dp-web4/ModuleCPU/SYNCHRONISM_PRINCIPLES.md

# ModuleCPU - Synchronism-Inspired Design Patterns

**Platform**: ATmega64M1 (8-bit AVR with CAN, 64KB flash, 4KB RAM)
**Role**: Middle management layer demonstrating hierarchical coordination

---

## Overview

ModuleCPU's architecture reflects several design patterns that align with principles described in the [Synchronism](https://github.com/dp-web4/Synchronism) framework. While fundamentally a battery management controller, its hierarchical design, autonomous operation, and interface boundaries can be viewed through the lens of distributed intelligence concepts.

This document explores these parallels - not as claims that ModuleCPU "embodies" philosophical principles, but as observations that certain system design patterns recur across scales from philosophy to embedded code.

---

## Design Patterns Aligned with Synchronism Concepts

### 1. Scale-Based Coordination

**Observation**: The module operates at an intermediate scale, coordinating subordinate elements while being coordinated by a superior layer

**Implementation**:
```
Pack Controller (Superior Scale)
    ↓ Provides constraints
ModuleCPU (This Scale)
    ↓ Coordinates subordinates
94 CellCPUs (Subordinate Scale)
```

**Autonomous Behavior at Module Scale**:
- Decides when to poll cells (timing strategy)
- Determines how to aggregate 94 cell readings
- Handles VUART communication errors locally
- Manages state transitions within constraints

**Constraints from Pack** (doesn't micromanage):
- Maximum allowed state (OFF/STANDBY/ACTIVE)
- Balancing permission
- Registration requirement

**Constraints from Cells** (physical limits):
- VUART timing and protocol
- Cell capability limits

**Pattern**: Each scale has autonomy within boundaries set by adjacent scales. This resembles the "scale-based autonomy" concept where each layer operates independently within its context.

---

### 2. Interface Boundaries as Information Filters

**Observation**: ModuleCPU has well-defined interfaces that hide internal complexity

**Upward Interface** (to Pack Controller):
```
Pack Controller sees:
- Module-level aggregates (average temp, voltage spread)
- Module state (OFF/STANDBY/ACTIVE/BALANCE)
- Cell count and communication statistics
- Error flags

Pack Controller does NOT see:
- Individual cell polling sequence
- VUART bit timing details
- Internal state machine transitions
- Individual cell raw data (until requested)
```

**Downward Interface** (to Cells):
```
Cells see:
- VUART requests for data
- Simple protocol (position in chain, data requests)

Cells do NOT see:
- CAN bus communication
- Pack Controller existence
- Other modules
- Module's internal decision logic
```

**Pattern**: These interface boundaries can be understood as analogous to "Markov blankets" - each layer sees only the interface of adjacent layers, not internal states.

---

### 3. Hierarchical Information Aggregation

**Observation**: Information compresses as it moves up the hierarchy

**Data Flow Upward** (Compression):
```
Cell Level: 94 cells × 2 sensors = 188 data points
    ├─ Cell 1: 23.5°C, 3.650V
    ├─ Cell 2: 23.7°C, 3.645V
    ├─ ...
    └─ Cell 94: 23.6°C, 3.655V

    ↓ (Module aggregates)

Module Level: Compressed to ~10 values
    ├─ Avg temp: 23.6°C
    ├─ Min voltage: 3.640V
    ├─ Max voltage: 3.660V
    ├─ Voltage spread: 20mV
    └─ Cell status bitmap

    ↓ (To Pack)

Pack sees: Summary, not raw data
```

**Inverse Command Flow** (Expansion):
```
Pack: "Enter BALANCE state" (1 command)
    ↓ (Module interprets)
Module: Polls 94 cells, sends balancing enable to subset
    ↓ (Cells execute)
Cells: Individual cells activate/deactivate FETs based on local voltage
```

**Pattern**: This asymmetric information flow (aggregation up, expansion down) resembles the hierarchical information dynamics described in distributed systems theory.

---

### 4. Emergent Coordination

**Observation**: System-level behavior emerges from local decisions without centralized control

**Example: Battery Balancing**

**No Central Balancing Controller**:
```c
// Module doesn't command: "Cell 5, balance at 50% duty cycle"
// Instead, module enables balancing context:

void EnableBalancing(void) {
    // Module simply requests cells to check their voltage
    for (uint8_t i = 0; i < cell_count; i++) {
        VUARTPollCell(i);  // Cell decides locally if it needs balancing
    }
}

// Each cell makes LOCAL decision:
// In CellCPU:
// if (my_voltage > threshold) { activate_balancing_FET(); }
```

**Emergent Result**:
- High cells balance (local decision)
- Module coordinates timing (when to poll)
- Pack enables context (permission to balance)
- **System-level balancing emerges** from distributed local decisions

**Pattern**: Intelligence emerges from coordination of simple autonomous elements, rather than centralized command-and-control.

---

### 5. Reality Construction Through Sensor Fusion

**Observation**: Module constructs a "view of reality" by fusing multiple data sources across time

**Temporal Sensor Fusion**:
```
Sensor Inputs (across time):
├─ Cell 1 temp (now): 23.5°C
├─ Cell 1 temp (1s ago): 23.4°C
├─ Cell 1 temp (2s ago): 23.3°C
│   ↓ (fusion across time)
└─ Derived: Temperature rising at 0.1°C/s

Multi-Cell Spatial Fusion:
├─ Cells 1-10 (top of module): 24.2°C average
├─ Cells 11-84 (middle): 23.6°C average
├─ Cells 85-94 (bottom): 23.0°C average
│   ↓ (spatial fusion)
└─ Derived: Thermal gradient of 1.2°C across module
```

**Emergent "Module Health" Concept**:
```c
// Module constructs emergent understanding
bool IsModuleHealthy(void) {
    float temp_avg = CalculateAverageTemp();
    float temp_spread = CalculateMaxTempDelta();
    float voltage_spread = CalculateMaxVoltageDelta();

    // "Health" emerges from fusion of multiple metrics
    return (temp_spread < 5.0) &&     // Temperature uniformity
           (voltage_spread < 0.050) &&  // Voltage balance
           (temp_avg < 60.0);           // Thermal safety
}
```

**Pattern**: Higher-level concepts ("module health") emerge from fusion of lower-level sensor data, similar to how reality might be constructed through sensor fusion in Synchronism's framework.

---

### 6. Intent Propagation Through Scales

**Observation**: System goals propagate through hierarchy, adapted at each scale

**Example: "Charge the Battery" Intent Flow**

```
User Intent: "Charge the battery"
    ↓
Pack Controller: Closes charging contactor, enables modules
    ↓ (propagates as)
Pack Command: "Modules, enter ACTIVE state"
    ↓
ModuleCPU: Transitions to ACTIVE, begins cell monitoring
    ↓ (propagates as)
Module Action: Polls cells, checks for overcharge
    ↓
CellCPU: Measures rising voltage
    ↓ (triggers local intent)
Cell Response: If voltage > threshold, activate balancing
```

**Intent Transforms at Each Scale**:
- **User scale**: "Charge"
- **Pack scale**: "Enable charging circuit"
- **Module scale**: "Monitor cells actively"
- **Cell scale**: "Measure and respond to voltage"

Each scale interprets and adapts the intent appropriate to its context.

---

## Practical Design Insights

These pattern observations lead to concrete design benefits:

### 1. Robustness Through Hierarchy

**Pattern**: Failures are contained within their scale

```
Cell Failure:
├─ Cell 23 stops responding
├─ Module detects missing cell (bitmap update)
├─ Module continues with 93 cells
├─ Pack sees module with reduced capacity
└─ System continues operating (degraded but functional)

Not: Entire system failure from one cell
```

### 2. Flexibility Through Interface Abstraction

**Pattern**: Implementation changes don't propagate across boundaries

```
Change Cell Temperature Sensor (MCP9843 → different sensor):
├─ Cell firmware changes (new I2C protocol)
├─ VUART interface unchanged (still transmits temperature)
├─ Module sees same data format
├─ Pack sees same module interface
└─ System continues working (transparent change)
```

### 3. Testability Through Scale Isolation

**Pattern**: Each scale can be tested independently

```
Module Testing:
├─ Can test with real cells (integration test)
├─ Can test with cell simulators (unit test)
├─ Can test with Pack or standalone (flexible context)
└─ Module logic testable without full system
```

---

## Code Examples Illustrating Patterns

### 1. Autonomous Decision Making (Scale-Based Autonomy)

```c
// Module decides HOW to handle communication errors
// Pack doesn't micromanage retry logic
void PollCellWithRetry(uint8_t cell_index) {
    uint8_t retry_count = 0;

    while (retry_count < MAX_RETRIES) {
        if (VUARTPollCell(cell_index)) {
            // Success - local decision to exit retry loop
            return;
        }

        // Local decision: exponential backoff
        _delay_ms(10 * (1 << retry_count));
        retry_count++;
    }

    // Local decision: mark cell as non-responsive
    UpdateCellStatus(cell_index, CELL_NO_RESPONSE);
}
```

### 2. Information Aggregation (Hierarchical Compression)

```c
// Module compresses 94 cells → summary for Pack
void PrepareModuleStatus(CANMessage* msg) {
    // Aggregate cell data
    float temp_avg = 0, temp_min = 999, temp_max = -999;
    uint16_t volt_min = 65535, volt_max = 0;

    for (uint8_t i = 0; i < cell_count; i++) {
        // Fusion across cells
        temp_avg += cell_temps[i];
        temp_min = min(temp_min, cell_temps[i]);
        temp_max = max(temp_max, cell_temps[i]);
        volt_min = min(volt_min, cell_voltages[i]);
        volt_max = max(volt_max, cell_voltages[i]);
    }
    temp_avg /= cell_count;

    // Pack message: compressed representation
    msg->data[0] = (uint8_t)(temp_avg);
    msg->data[1] = (uint8_t)(temp_max - temp_min);  // Spread, not individuals
    msg->data[2] = volt_min >> 8;
    msg->data[3] = volt_min & 0xFF;
    msg->data[4] = (volt_max - volt_min) >> 8;  // Delta, not absolutes
    msg->data[5] = (volt_max - volt_min) & 0xFF;

    // 188 values compressed to 6 bytes
}
```

### 3. Interface Boundary (Markov Blanket-Style)

```c
// Module's interface to Pack: well-defined, hides internals
void ProcessPackCommand(CANMessage* cmd) {
    switch (cmd->id) {
        case ID_MODULE_STATE_CHANGE:
            // Pack can request state change
            // Module decides if transition is valid
            if (CanTransitionTo(cmd->data[0])) {
                ChangeState(cmd->data[0]);
            } else {
                // Internal logic: reject invalid transition
                SendErrorResponse();
            }
            break;

        case ID_MODULE_STATUS_REQUEST:
            // Pack requests status
            // Module decides what to include based on current state
            SendStatusMessage();
            break;

        // Pack doesn't have commands for:
        // - "Poll cell 23 right now"
        // - "Set VUART timing to X"
        // - "Use this specific aggregation algorithm"
        // Module retains autonomy over internal operations
    }
}
```

---

## Relationship to Synchronism Whitepaper

Readers interested in the theoretical foundations that inform these design patterns may find relevant concepts in the [Synchronism Whitepaper](https://github.com/dp-web4/Synchronism):

- **Section on Intent Dynamics**: How goals propagate and transform across scales
- **Section on Markov Blankets**: Information boundaries and interface design
- **Section on Scale-Based Autonomy**: Hierarchical coordination without micromanagement
- **Section on Sensor Fusion**: How reality emerges from integrated data sources

These are offered as conceptual frameworks that may provide useful lenses for understanding embedded system architecture, not as claims that a battery controller implements abstract philosophy.

---

## Summary

ModuleCPU's design exhibits several patterns that align with concepts from distributed systems theory and the Synchronism framework:

1. **Scale-Based Autonomy**: Module operates independently within constraints
2. **Interface Boundaries**: Well-defined information hiding at each layer
3. **Hierarchical Aggregation**: Information compresses upward, commands expand downward
4. **Emergent Coordination**: System behavior from distributed local decisions
5. **Sensor Fusion**: Higher-level understanding from integrated data
6. **Intent Propagation**: Goals transform appropriately at each scale

These patterns emerged from practical engineering requirements (managing 94 cells efficiently, maintaining robustness, enabling testability) but happen to parallel theoretical concepts in interesting ways.

**Whether viewed as philosophy-in-silicon or simply sound embedded system design, these patterns demonstrably work in production hardware.**
