dp-web4/ModuleCPU/.github/TOPICS.md

# Repository Topics

## Primary Topics
- battery-management-system
- bms
- embedded-systems
- modbatt
- battery

## Platform/Hardware
- atmega64m1
- avr
- can-bus
- module-controller

## Architecture/Patterns
- distributed-intelligence
- hierarchical-control
- aggregation
- virtual-uart
- markov-blanket
- fractal-architecture

## Application Domain
- electric-vehicle
- lithium-ion
- energy-storage
- iot

## Ecosystem/Framework
- web4
- synchronism
- open-source
- agpl-3.0

## Use these topics on GitHub via Settings → Topics
