dp-web4/ModuleCPU/can.c

/* 
 * Module controller firmware - CAN
 *
 * This module contains the CAN bus functionality. 
 *
 */

#include <stdint.h>
#include <xc.h>
#include <stdbool.h>
#include <avr/interrupt.h>
#include <string.h>
#include "main.h"
#include "can.h"
#include "can_ids.h"
#include "vUART.h"  // For vUARTIsBusy()

#define CAN_DISABLED			(0)
#define CAN_TXONLY				(1)
#define CAN_RXONLY				(2)
#define CAN_FBRX				(3)

#define CANMOB_RX_IDX			(0)
#define CANMOB_TX_IDX			(1)

// Timeout for CAN TX in main loop ticks (100ms each)
#define CAN_TX_TIMEOUT_TICKS	(2)	// 200ms timeout

static volatile uint8_t sg_u8Busy;	// 0 = not busy, >0 = busy with timeout countdown
static void (*sg_pfRXCallback)(ECANMessageType eType, uint8_t* pu8Data, uint8_t u8DataLen);

// Maximum size of CAN message
#define CAN_MAX_MSG_SIZE		8

// Last transmit info
static uint8_t sg_u8TransmitAttempts;
static ECANMessageType sg_eLastTXType;
static uint8_t sg_u8LastTXData[CAN_MAX_MSG_SIZE];
static uint8_t sg_u8LastTXDataLen;
static volatile bool sg_bInRetransmit = false;

// Diagnostic counters for CAN issues
static uint16_t sg_u16TxTimeouts = 0;		// Count of TX timeouts
static uint16_t sg_u16TxErrors = 0;		// Count of TX errors recovered
static uint16_t sg_u16TxOkPolled = 0;		// Count of TXOK found by polling
static uint16_t sg_u16BusOffEvents = 0;	// Count of bus-off events
static uint16_t sg_u16ErrorPassive = 0;	// Count of error passive states
static uint8_t sg_u8BusOffRecoveryDelay = 0;	// Delay counter after bus-off recovery
static uint8_t sg_u8TxOnlyErrorCount = 0;	// Count of consecutive TX-only errors
static uint8_t sg_u8TxBackoffDelay = 0;	// Adaptive backoff delay for TX errors

// RX Message Queue - moves heavy processing out of ISR to main loop
#define CAN_RX_QUEUE_SIZE 8
typedef struct {
	ECANMessageType eType;
	uint8_t u8Data[CAN_MAX_MSG_SIZE];
	uint8_t u8DataLen;
} CANRxMessage;

static CANRxMessage sg_rxQueue[CAN_RX_QUEUE_SIZE];
static volatile uint8_t sg_rxQueueHead = 0;
static volatile uint8_t sg_rxQueueTail = 0;
static uint16_t sg_u16RxQueueOverflows = 0;	// Diagnostic: queue overflow count

// MOB Reconfiguration Flags - defers MOB setup to main loop
static volatile bool sg_bMOB0NeedsReconfigure = false;
static volatile bool sg_bMOB2NeedsReconfigure = false;

// TX Retry Flag - defers retry logic to main loop
static volatile bool sg_bRetryPending = false;

typedef struct 
{
	uint8_t u8Mode;
	bool bReplyValid;
	uint16_t u16ID;
	uint16_t u16IDMask;
	bool bRTRTag;
	bool bRTRMask;
} SMOBDef;

static const SMOBDef sg_sMOBDisabled =
{
	CAN_DISABLED,
	false,
	0x7ff,
	0x7ff,
	false,
	false,
};

// Recevie any message with ID 0x5xx (RTR or not)
static const SMOBDef sg_sMOBGenericReceive =
{
	CAN_RXONLY,
	false,
	0x500,
	0x700,  // Mask: 0x700 = bits 10:8 must match, allowing only 0x500-0x5FF
	false,
	false,
};

static const SMOBDef sg_sMOBModuleAnnouncement =
{
	CAN_TXONLY,
	false,
	PKT_MODULE_ANNOUNCEMENT,
	0x7ff,
	false,
	false,
};

static const SMOBDef sg_sMOBModuleStatus1 =
{
	CAN_TXONLY,
	false,
	PKT_MODULE_STATUS1,
	0x7ff,
	false,
	false,
};

static const SMOBDef sg_sMOBModuleStatus2 =
{
	CAN_TXONLY,
	false,
	PKT_MODULE_STATUS2,
	0x7ff,
	false,
	false,
};

static const SMOBDef sg_sMOBModuleStatus3 =
{
	CAN_TXONLY,
	false,
	PKT_MODULE_STATUS3,
	0x7ff,
	false,
	false,
};

static const SMOBDef sg_sMOBModuleCellCommStat1 =
{
	CAN_TXONLY,
	false,
	PKT_MODULE_CELL_COMM_STAT1,
	0x7ff,
	false,
	false,
};

static const SMOBDef sg_sMOBModuleCellCommStat2 =
{
	CAN_TXONLY,
	false,
	PKT_MODULE_CELL_COMM_STAT2,
	0x7ff,
	false,
	false,
};

static const SMOBDef sg_sMOBModuleCellDetail = 
{
	CAN_TXONLY,
	false,
	PKT_MODULE_CELL_DETAIL,
	0x7ff,
	false,
	false,
};

static const SMOBDef sg_sMOBModuleHardwareDetail = 
{
	CAN_TXONLY,
	false,
	PKT_MODULE_HARDWARE,
	0x7ff,
	false,
	false,
};

static const SMOBDef sg_sMOBModuleRequestTime =
{
	CAN_TXONLY,
	false,
	PKT_MODULE_REQUEST_TIME,
	0x7ff,
	false,
	false,
};

// Frame transfer MOBs
static const SMOBDef sg_sMOBFrameTransferStart =
{
	CAN_TXONLY,
	false,
	PKT_FRAME_TRANSFER_START,
	0x7ff,
	false,
	false,
};

static const SMOBDef sg_sMOBFrameTransferData =
{
	CAN_TXONLY,
	false,
	PKT_FRAME_TRANSFER_DATA,
	0x7ff,
	false,
	false,
};

static const SMOBDef sg_sMOBFrameTransferEnd =
{
	CAN_TXONLY,
	false,
	PKT_FRAME_TRANSFER_END,
	0x7ff,
	false,
	false,
};


typedef struct  
{
	uint16_t u16ID;
	ECANMessageType eType;
} SCANCmdReg;

static const SCANCmdReg sg_sRXCommandList[] =
{
	{PKT_MODULE_REGISTRATION,	ECANMessageType_ModuleRegistration},
	{PKT_MODULE_DETAIL_REQUEST, ECANMessageType_ModuleCellDetailRequest},
	{PKT_MODULE_STATE_CHANGE,	ECANMessageType_ModuleStateChangeRequest},
	{PKT_MODULE_STATUS_REQUEST, ECANMessageType_ModuleStatusRequest},
	{PKT_MODULE_HARDWARE_REQUEST, ECANMessageType_ModuleHardwareDetail},
	{PKT_MODULE_ANNOUNCE_REQUEST, ECANMessageType_ModuleAnnounceRequest},
	{PKT_MODULE_DEREGISTER,     ECANMessageType_ModuleDeRegister},
	{PKT_MODULE_ALL_DEREGISTER, ECANMessageType_AllDeRegister},
	{PKT_MODULE_ALL_ISOLATE,	ECANMessageType_AllIsolate},
	{PKT_MODULE_SET_TIME,		ECANMessageType_SetTime},
	{PKT_MODULE_MAX_STATE,		ECANMessageType_MaxState},
	{PKT_FRAME_TRANSFER_REQUEST, ECANMessageType_FrameTransferRequest}
};

static ECANMessageType CANLookupCommand( uint16_t u16ID )
{
	uint8_t u8Index = 0;
	
	while( u8Index < (sizeof(sg_sRXCommandList)/sizeof(sg_sRXCommandList[0])) )
	{
		if( sg_sRXCommandList[u8Index].u16ID == u16ID )
		{
			return( sg_sRXCommandList[u8Index].eType );
		}
		
		u8Index++;
	}
	
	return( ECANMessageType_MAX );
}

static void CANMOBSetWithSeq( uint8_t u8MOBIndex,
					   const SMOBDef* psDef,
					   uint8_t* pu8Data,
					   uint8_t u8DataLen,
					   uint16_t u16SeqNum )
{
	uint8_t u8CANCDMOBValue;
	uint32_t u32MessageID;
	uint8_t savedCANGIE;

	MBASSERT( u8MOBIndex <= 5 );
	MBASSERT( u8DataLen <= 8 );

	// Disable CAN interrupts during MOB configuration to prevent corruption
	savedCANGIE = CANGIE;
	CANGIE &= ~(1 << ENIT);

	// Set the MOB page, auto increment, and data index 0
	CANPAGE = u8MOBIndex << 4;

	// Clear the MOB status
	CANSTMOB = 0;

	// Set the MOB registers for this page
	u8CANCDMOBValue = u8DataLen;
	u8CANCDMOBValue |= (psDef->u8Mode << CONMOB0);
	if( psDef->bReplyValid )
	{
		u8CANCDMOBValue |= (1 << RPLV);
	}
	u8CANCDMOBValue |= (1 << IDE);

	// Extended frame address format
	//	Bits 0-7: Pack / Module registration ID of sender (if assigned, zero otherwise)
	//	Bits 8-17: Sequence number (for frame transfer DATA messages, 0-127)
	//	Bits 18-28: Static message ID (eg. 0x500)

	u32MessageID = (uint32_t)PlatformGetRegistrationID();
	u32MessageID |= ((uint32_t)(u16SeqNum & 0x3FF)) << 8;  // Sequence in bits 8-17
	u32MessageID |= (((uint32_t)psDef->u16ID) & 0x7ff) << 18;

	// Set the ID registers
	CANIDT4 = psDef->bRTRTag?(1 << RTRTAG):0;
	CANIDT4 |= u32MessageID << 3;
	CANIDT3 = u32MessageID >> 5;
	CANIDT2 = u32MessageID >> 13;
	CANIDT1 = u32MessageID >> 21;

	// Setup mask for the cmd (require matching ID extention bit)
	CANIDM4 = psDef->bRTRMask?(1 << RTRTAG):0;
	CANIDM4 |= (1 << IDEMSK);
	CANIDM3 = 0;
	CANIDM2 = psDef->u16IDMask << 5;
	CANIDM1 = psDef->u16IDMask >> 3;

	// Set the data into the FIFO
	while( u8DataLen )
	{
		CANMSG = *pu8Data;

		pu8Data++;
		u8DataLen--;
	}

	// Send it now
	CANCDMOB = u8CANCDMOBValue;

	// Enable (activates the MOB) or disable the MOB interrupt
	if( psDef->u8Mode != CAN_DISABLED )
	{
		CANIE2 |= (1 << u8MOBIndex);
	}
	else
	{
		CANIE2 &= (uint8_t)~(1 << u8MOBIndex);
	}

	// Restore CAN interrupts
	CANGIE = savedCANGIE;
}

static void CANMOBSet( uint8_t u8MOBIndex,
					   const SMOBDef* psDef,
					   uint8_t* pu8Data,
					   uint8_t u8DataLen )
{
	// Call the version with sequence number = 0
	CANMOBSetWithSeq(u8MOBIndex, psDef, pu8Data, u8DataLen, 0);
}

static void CANSendMessageInternal( ECANMessageType eType,
									uint8_t* pu8Data,
									uint8_t u8DataLen,	
									bool bRetransmit )
{
	const SMOBDef* psDef = NULL;
	
	if( ECANMessageType_ModuleAnnouncement == eType )
	{
		psDef = &sg_sMOBModuleAnnouncement;
	}
	else if( ECANMessageType_ModuleStatus1 == eType )
	{
		psDef = &sg_sMOBModuleStatus1;
	}
	else if( ECANMessageType_ModuleStatus2 == eType )
	{
		psDef = &sg_sMOBModuleStatus2;
	}
	else if( ECANMessageType_ModuleStatus3 == eType )
	{
		psDef = &sg_sMOBModuleStatus3;
	}
	else if( ECANMessageType_ModuleCellCommStat1 == eType )
	{
		psDef = &sg_sMOBModuleCellCommStat1;
	}
	else if( ECANMessageType_ModuleCellCommStat2 == eType )
	{
		psDef = &sg_sMOBModuleCellCommStat2;
	}
	else if( ECANMessageType_ModuleHardwareDetail == eType )
	{
		psDef = &sg_sMOBModuleHardwareDetail;
	}
	else if( ECANMessageType_ModuleCellDetail == eType )
	{
		psDef = &sg_sMOBModuleCellDetail;
	}
	else if( ECANMessageType_ModuleRequestTime == eType )
	{
		psDef = &sg_sMOBModuleRequestTime;
	}
	else if( ECANMessageType_FrameTransferStart == eType )
	{
		psDef = &sg_sMOBFrameTransferStart;
	}
	else if( ECANMessageType_FrameTransferData == eType )
	{
		psDef = &sg_sMOBFrameTransferData;
	}
	else if( ECANMessageType_FrameTransferEnd == eType )
	{
		psDef = &sg_sMOBFrameTransferEnd;
	}
	else
	{
		// Invalid message type
		MBASSERT(0);
	}
	
	if(bRetransmit && sg_bInRetransmit) {
		// Already in a retransmit, don't allow nested retries
		return;
	}
	if( bRetransmit || (0 == sg_u8Busy) )
	{
		// Only reset timeout if not already busy, or if explicitly retransmitting
		// Don't extend timeout on retransmits - use existing countdown
		if (0 == sg_u8Busy)
		{
			sg_u8Busy = CAN_TX_TIMEOUT_TICKS;
		}
		
		// Save this message info for retransmit later if needed
		if( false == bRetransmit )
		{
			sg_u8TransmitAttempts = 0;
			sg_eLastTXType = eType;
			MBASSERT(u8DataLen <= CAN_MAX_MSG_SIZE);
			memcpy(sg_u8LastTXData, pu8Data, u8DataLen);
			sg_u8LastTXDataLen = u8DataLen;
		}
		else
		{
			sg_u8TransmitAttempts++;
		}
		
		// Send it now
		CANMOBSet( CANMOB_TX_IDX, psDef, pu8Data, u8DataLen );
	}
}

static void CANSendMessageInternalWithSeq( ECANMessageType eType,
									uint8_t* pu8Data,
									uint8_t u8DataLen,
									uint16_t u16SeqNum,
									bool bRetransmit )
{
	const SMOBDef* psDef = NULL;

	if( ECANMessageType_ModuleAnnouncement == eType )
	{
		psDef = &sg_sMOBModuleAnnouncement;
	}
	else if( ECANMessageType_ModuleStatus1 == eType )
	{
		psDef = &sg_sMOBModuleStatus1;
	}
	else if( ECANMessageType_ModuleStatus2 == eType )
	{
		psDef = &sg_sMOBModuleStatus2;
	}
	else if( ECANMessageType_ModuleStatus3 == eType )
	{
		psDef = &sg_sMOBModuleStatus3;
	}
	else if( ECANMessageType_ModuleCellCommStat1 == eType )
	{
		psDef = &sg_sMOBModuleCellCommStat1;
	}
	else if( ECANMessageType_ModuleCellCommStat2 == eType )
	{
		psDef = &sg_sMOBModuleCellCommStat2;
	}
	else if( ECANMessageType_ModuleHardwareDetail == eType )
	{
		psDef = &sg_sMOBModuleHardwareDetail;
	}
	else if( ECANMessageType_ModuleCellDetail == eType )
	{
		psDef = &sg_sMOBModuleCellDetail;
	}
	else if( ECANMessageType_ModuleRequestTime == eType )
	{
		psDef = &sg_sMOBModuleRequestTime;
	}
	else if( ECANMessageType_FrameTransferStart == eType )
	{
		psDef = &sg_sMOBFrameTransferStart;
	}
	else if( ECANMessageType_FrameTransferData == eType )
	{
		psDef = &sg_sMOBFrameTransferData;
	}
	else if( ECANMessageType_FrameTransferEnd == eType )
	{
		psDef = &sg_sMOBFrameTransferEnd;
	}
	else
	{
		// Invalid message type
		MBASSERT(0);
	}

	if(bRetransmit && sg_bInRetransmit) {
		// Already in a retransmit, don't allow nested retries
		return;
	}
	if( bRetransmit || (0 == sg_u8Busy) )
	{
		// Only reset timeout if not already busy, or if explicitly retransmitting
		// Don't extend timeout on retransmits - use existing countdown
		if (0 == sg_u8Busy)
		{
			sg_u8Busy = CAN_TX_TIMEOUT_TICKS;
		}

		// Save this message info for retransmit later if needed
		if( false == bRetransmit )
		{
			sg_u8TransmitAttempts = 0;
			sg_eLastTXType = eType;
			MBASSERT(u8DataLen <= CAN_MAX_MSG_SIZE);
			memcpy(sg_u8LastTXData, pu8Data, u8DataLen);
			sg_u8LastTXDataLen = u8DataLen;
		}
		else
		{
			sg_u8TransmitAttempts++;
		}

		// Send it now with sequence number
		CANMOBSetWithSeq( CANMOB_TX_IDX, psDef, pu8Data, u8DataLen, u16SeqNum );
	}
}

/*
 * CAN MOB Interrupt Handler Flow Documentation
 * =============================================
 * 
 * NORMAL TX FLOW:
 * 1. CANSendMessage() called by application
 * 2. CANSendMessageInternal() prepares message
 * 3. CANMOBSet() configures TX MOB and enables CANIE2 interrupt (line 266)
 * 4. TX completes, interrupt fires, this handler called
 * 5. TX MOB handler disables MOB (line 359-360) but does NOT re-enable
 * 6. Next TX: CANMOBSet() called again, re-enables CANIE2
 * 
 * TX ERROR/RETRY FLOW:
 * 1. TX error occurs (collision, ACK error, etc.)
 * 2. This handler detects error in TX MOB section
 * 3. If retries available, calls CANSendMessageInternal() directly
 * 4. CANSendMessageInternal() calls CANMOBSet() which re-enables MOB
 * 5. If retries exhausted, clears sg_bBusy but MOB stays disabled
 * 
 * NORMAL RX FLOW:
 * 1. At init, CANMOBSet() configures RX MOB with receive filter
 * 2. CANIE2 enabled for RX MOB (line 266 in CANMOBSet)
 * 3. Message arrives matching filter, interrupt fires
 * 4. RX MOB handler disables MOB temporarily (line 359-360)
 * 5. Handler extracts message data, calls callback
 * 6. Handler re-enables RX MOB at end (line 430-431)
 * 7. Ready to receive next message
 * 
 * IMPORTANT NOTES:
 * - TX MOB is one-shot, gets re-enabled only when next TX is set up
 * - RX MOB is continuous, gets re-enabled immediately after processing
 * - System works because CANMOBSet() always re-enables on next TX
 * - Potential issue: TX MOB stays disabled after last transmission
 */
void CANMOBInterrupt( uint8_t u8MOBIndex )
{
	// Set the MOB page first (and zero the data index)
	CANPAGE = u8MOBIndex << 4;
	
	// Temporarily disable the MOB to examine and modify the registers
	CANIE2 &= (uint8_t)~(1 << u8MOBIndex);
	CANCDMOB &= (uint8_t)~((1 << CONMOB0) | (1 << CONMOB1));
	
	if( CANMOB_RX_IDX == u8MOBIndex )
	{
		// CRITICAL FIX: RX MOB should NOT handle TX status bits at all!
		// This entire TX handling block in RX context is wrong and has been removed.
		// If TXOK appears in RX MOB, it's likely a hardware quirk or misconfiguration,
		// but handling it here can interfere with actual TX operations.
		// TX status should ONLY be handled in TX MOB context (CANMOB_TX_IDX).
		/*
		// TX success?  Just clear it since this is the RX context
		if( CANSTMOB & (1 << TXOK) )
		{
			// Clear it
			CANSTMOB &= ~(1 << TXOK);
			// CRITICAL BUG FIX: Do NOT clear sg_bBusy or sg_bInRetransmit here!
			// This is the RX MOB context, not TX. Clearing these flags here causes race conditions
			// where new TX can start while previous TX is still in progress, leading to
			// CAN peripheral confusion and module lockups. TX completion is properly handled
			// in the TX MOB context (CANMOB_TX_IDX) at line 428.
			// sg_bBusy = false;  // WRONG - commented out to fix CAN reliability issues
			// sg_bInRetransmit = false;  // WRONG - also should not be cleared here
		}
		*/
		// RX success?
		if( CANSTMOB & (1 << RXOK) )
		{
			// Clear it
			CANSTMOB &= ~(1 << RXOK);

			if( sg_pfRXCallback )
			{
				ECANMessageType eType;
				uint16_t u16ID = 0;
				uint8_t u8Data[8];
				uint8_t u8DataLen = CANCDMOB & 0x0f;
				uint8_t u8Index = 0;

				// Grab the messageID from the identifier registers
				// TODO: This extraction may be wrong for extended frames
				// but it worked with the real Pack Controller somehow
				u16ID = ((uint16_t)CANIDT1) << 3;
				u16ID |= CANIDT2 >> 5;

				// Pull the data out into a temp buffer
				while( u8Index < u8DataLen )
				{
					u8Data[u8Index] = CANMSG;
					u8Index++;
				}

				// Lookup ID to see if it matches one of ours
				eType = CANLookupCommand( u16ID );

				if( eType != ECANMessageType_MAX )
				{
					// Queue the message for processing in main loop instead of calling callback in ISR
					// This dramatically reduces ISR duration and prevents VUART timing interference
					uint8_t nextHead = (sg_rxQueueHead + 1) % CAN_RX_QUEUE_SIZE;
					if (nextHead != sg_rxQueueTail)  // Queue not full
					{
						sg_rxQueue[sg_rxQueueHead].eType = eType;
						sg_rxQueue[sg_rxQueueHead].u8DataLen = u8DataLen;
						memcpy(sg_rxQueue[sg_rxQueueHead].u8Data, u8Data, u8DataLen);
						sg_rxQueueHead = nextHead;
					}
					else
					{
						// Queue overflow - message dropped
						sg_u16RxQueueOverflows++;
					}
				}
			}
		}
	
		// If receive error, clear the bits
		if( CANSTMOB & ((1 << SERR) | (1 << CERR) | (1 << FERR)) )
		{
			// Clear it.  Just ignore
			CANSTMOB &= ~((1 << SERR) | (1 << CERR) | (1 << FERR));
		}
	
		// Re-enable RX now
		CANIE2 |= (1 << u8MOBIndex);
		CANCDMOB |= (1 << CONMOB1);
	}
	else if( CANMOB_TX_IDX == u8MOBIndex )
	{
		if( CANSTMOB & (1 << TXOK) )
		{
			// Clear it
			CANSTMOB &= ~(1 << TXOK);

			sg_u8Busy = 0;
		}
		
		// RX success, just clear it since this is the TX context
//		if( CANSTMOB & (1 << RXOK) )
//		{
			// Clear it
//			CANSTMOB &= ~(1 << RXOK);
//		}

		// If TX Error on transmit (collision with another device)
		// -or- ACK error (nobody listening),
		// defer retry to main loop
		if( CANSTMOB & ((1 << BERR) | (1 << AERR) | (1 << SERR)) )
		{
			// Clear it
			CANSTMOB &= ~((1 << BERR) | (1 << AERR) | (1 << SERR));

			if( sg_u8TransmitAttempts < 20 )
			{
				// Set flag to retry in main loop (reduces ISR duration)
				sg_bRetryPending = true;
			}
			else
			{
				// Retries exhausted.  Give up
				sg_u8Busy = 0;
				sg_bInRetransmit = false;
			}
		}
	}
}

// Generic CAN interrupt handler
// Check interrrupt sources and clear them (by servicing or explicit clearing)
ISR(CAN_INT_vect, ISR_BLOCK)
{
	// Save state we'll need to restore
	uint8_t saved_cangie = CANGIE;
	uint8_t saved_canie2 = CANIE2;	// Temporarily disable CAN interrupts to prevent reentry
	CANGIE &= (uint8_t)~(1 << ENIT);

	// Do NOT re-enable global interrupts - this causes race conditions!
	
	 uint8_t sit = CANSIT2;

	 // Most common interrupts first  *claude
	 // Check MOB 0 (module-specific RX)
	 if(sit & (1 << CANMOB_RX_IDX)) {
		 CANMOBInterrupt(CANMOB_RX_IDX);
		 sg_bMOB0NeedsReconfigure = true;  // Defer MOB reconfiguration to main loop
	 }

	 // Check MOB 2 (broadcast RX)
	 if(sit & (1 << 2)) {
		 CANMOBInterrupt(2);
		 sg_bMOB2NeedsReconfigure = true;  // Defer MOB reconfiguration to main loop
	 }

	// Check TX MOB
	if( sit & (1 << CANMOB_TX_IDX) )
	{
		CANMOBInterrupt( CANMOB_TX_IDX );
	}
	
	// Now the generic, non-MOB interrupts (some of which may have already been handled by the MOB handler)
	
	// Bus Off interrupt - CRITICAL: Must recover from bus-off state!
	if( CANGIT & (1 << BOFFIT) )
	{
		// Clear the interrupt flag
		CANGIT = (1 << BOFFIT);

		// Increment diagnostic counter
		sg_u16BusOffEvents++;

		// CRITICAL: Re-enable the CAN controller after bus-off
		// The controller automatically enters "disabled" state on bus-off
		// and must be manually re-enabled
		CANGCON = (1 << ENASTB);

		// Clear busy flag since any pending transmission is lost
		sg_u8Busy = 0;
		sg_bInRetransmit = false;

		// Set recovery delay - don't transmit for a while after bus-off
		// This gives the bus time to stabilize and prevents immediate re-entry to bus-off
		sg_u8BusOffRecoveryDelay = 10;	// 10 ticks = 1 second at 100ms/tick
	}
	
	// Frame buffer receive (burst receive interrupt)
	// This should not be used
	if( CANGIT & (1 << BXOK) )
	{
		MBASSERT(0);
		
		// TODO: Must write the CONMOB fields of the MOB that interrupted first?
		// Just clear it for now
		CANGIT = (1 << BXOK);
	}
	
	// Bit stuffing error on receive
	if( CANGIT & (1 << SERG) )
	{
		// Just clear it for now.  Ignored.
		CANGIT = (1 << SERG);
	}
	
	// CRC error on receive
	if( CANGIT & (1 << CERG) )
	{
		// Just clear it for now.  Ignored.
		CANGIT = (1 << CERG);
	}
	
	// Form error
	if( CANGIT & (1 << FERG) )
	{
		// If detected form error on transmit, could be duplicate to MOB error interrupt (see 16.8.2 - Interrupt Behavior)
		// Ignore this one
		
		// Just clear it for now.  Ignored.
		CANGIT = (1 << FERG);
	}
	
	// ACK missing on transmit (nobody's listening! (or failure on transmit???))
	if( CANGIT & (1 << AERG) )
	{
		// Clear the interrupt
		CANGIT = (1 << AERG);

		if( sg_u8TransmitAttempts < 20 )
		{
			// Set flag to retry in main loop (reduces ISR duration)
			sg_bRetryPending = true;
		}
		else
		{
			// Retries exhausted.  Give up
			sg_u8Busy = 0;
		}
	}

	// Reenable CAN general interrupt	
//	CANGIE |= (1 << ENIT);
    CANIE2 = saved_canie2;
    CANGIE = saved_cangie;
}

bool CANSendMessage( ECANMessageType eType,
					 uint8_t* pu8Data,
					 uint8_t u8DataLen )
{
	// VUART timing interference prevention - COMMENTED OUT
	// While this successfully eliminated scope-visible disruptions to VUART timing,
	// it severely disrupted CAN communications. Next-gen solution is faster processor.
	// For now, need to find alternate approach (priority adjustment, shorter ISRs, etc.)
	// if (vUARTIsBusy())
	// {
	//     return(false);
	// }

	// Don't transmit during bus-off recovery period
	if (sg_u8BusOffRecoveryDelay > 0)
	{
		return(false);
	}

	// Don't transmit during TX backoff period (adaptive backoff for persistent errors)
	if (sg_u8TxBackoffDelay > 0)
	{
		return(false);
	}

	// If we're busy, kick it back so we're cooperatively multitasking
	// rather than spin locking
	if (sg_u8Busy)
	{
		return(false);
	}

	CANSendMessageInternal( eType, pu8Data, u8DataLen, false );
	return( true );
}

bool CANSendMessageWithSeq( ECANMessageType eType,
						uint8_t* pu8Data,
						uint8_t u8DataLen,
						uint16_t u16SeqNum )
{
	// VUART timing interference prevention - COMMENTED OUT
	// While this successfully eliminated scope-visible disruptions to VUART timing,
	// it severely disrupted CAN communications. Next-gen solution is faster processor.
	// For now, need to find alternate approach (priority adjustment, shorter ISRs, etc.)
	// if (vUARTIsBusy())
	// {
	//     return(false);
	// }

	// Don't transmit during bus-off recovery period
	if (sg_u8BusOffRecoveryDelay > 0)
	{
		return(false);
	}

	// Don't transmit during TX backoff period (adaptive backoff for persistent errors)
	if (sg_u8TxBackoffDelay > 0)
	{
		return(false);
	}

	// If we're busy, kick it back so we're cooperatively multitasking
	// rather than spin locking
	if (sg_u8Busy)
	{
		return(false);
	}

	CANSendMessageInternalWithSeq( eType, pu8Data, u8DataLen, u16SeqNum, false );
	return( true );
}

void CANSetRXCallback( void (*pfCallback)(ECANMessageType eType, uint8_t* pu8Data, uint8_t u8DataLen) )
{
	sg_pfRXCallback = pfCallback;
}

void CANSetModuleIDFilter(uint8_t u8MOBIndex, uint8_t u8ModuleID)
{
	uint8_t savedCANGIE;
	uint32_t u32MessageID;

	MBASSERT(u8MOBIndex <= 5);

	// Disable CAN interrupts during MOB reconfiguration
	savedCANGIE = CANGIE;
	CANGIE &= ~(1 << ENIT);

	// Set MOB page
	CANPAGE = u8MOBIndex << 4;

	// Temporarily disable MOB
	CANIE2 &= ~(1 << u8MOBIndex);
	CANCDMOB &= ~((1 << CONMOB0) | (1 << CONMOB1));

	// Update extended ID filter (bits 0-7 = module ID)
	// Keep base ID (bits 18-28) at 0x500 with 0x700 mask
	u32MessageID = (uint32_t)u8ModuleID;
	u32MessageID |= (((uint32_t)0x500) & 0x7ff) << 18;

	CANIDT4 = u32MessageID << 3;
	CANIDT3 = u32MessageID >> 5;
	CANIDT2 = u32MessageID >> 13;
	CANIDT1 = u32MessageID >> 21;

	// Set mask: bits 0-7 must match exactly (0xFF), bits 18-28 use 0x700 mask
	CANIDM4 = (1 << IDEMSK);  // Extended frame mask
	CANIDM4 |= 0xFF << 3;     // Module ID bits 0-7 must match exactly
	CANIDM3 = 0xFF >> 5;      // Continue module ID mask
	CANIDM2 = 0x700 << 5;     // Base ID mask
	CANIDM1 = 0x700 >> 3;

	// Re-enable RX mode
	CANCDMOB = 8 | (1 << CONMOB1) | (1 << IDE);  // 8 bytes, RX mode, extended frame
	CANIE2 |= (1 << u8MOBIndex);

	// Restore CAN interrupts
	CANGIE = savedCANGIE;
}

void CANInit( void )
{
	// Init clock
	// See datasheet table 16-2.
	// For 8Mhz, set CAN rate to 500 Kbps
	CANBT1 = 0x02;
	CANBT2 = 0x04;
	CANBT3 = 0x12;
	
	// Init message objects (MOBs) since there are no defaults at reset
	CANMOBSet( 0, &sg_sMOBDisabled, NULL, 0 );
	CANMOBSet( 1, &sg_sMOBDisabled, NULL, 0 );
	CANMOBSet( 2, &sg_sMOBDisabled, NULL, 0 );
	CANMOBSet( 3, &sg_sMOBDisabled, NULL, 0 );
	CANMOBSet( 4, &sg_sMOBDisabled, NULL, 0 );
	CANMOBSet( 5, &sg_sMOBDisabled, NULL, 0 );

	// Setup MOB 0 for module-specific RX (unregistered = 0xFF)
	CANMOBSet( CANMOB_RX_IDX, &sg_sMOBGenericReceive, NULL, 0 );
	CANSetModuleIDFilter( CANMOB_RX_IDX, 0xFF );

	// Setup MOB 2 for broadcast RX (always 0x00)
	CANMOBSet( 2, &sg_sMOBGenericReceive, NULL, 0 );
	CANSetModuleIDFilter( 2, 0x00 );
	
	// Enable general CAN interrupts
	CANGIE = (1 << ENIT) | (1 << ENRX) | (1 << ENTX) | (1 << ENERR) | (1 << ENBX) | (1 << ENERG);

//	CANGIE &= ~(1 << ENOVRT);  // Disable CAN timer overflow interrupt

	// Enable the bus
	CANGCON = (1 << ENASTB);
	sg_u8Busy = 0;
}

void CANCheckTxStatus(void)
{
	// Only check if we think we're busy
	if (sg_u8Busy > 0)
	{
		// Save current MOB and switch to TX MOB
		uint8_t savedMOB = CANPAGE;
		CANPAGE = CANMOB_TX_IDX << MOBNB0;

		// Check if transmission completed successfully
		if (CANSTMOB & (1 << TXOK))
		{
			// Clear the flag
			CANSTMOB &= ~(1 << TXOK);
			sg_u8Busy = 0;
			sg_u16TxOkPolled++;	// Diagnostic: we caught TXOK by polling
		}
		// Check for transmission errors
		else if (CANSTMOB & ((1 << BERR) | (1 << SERR) | (1 << CERR) | (1 << FERR) | (1 << AERR)))
		{
			// Clear all error flags and reset busy flag
			CANSTMOB = 0x00;
			sg_u8Busy = 0;
			sg_u16TxErrors++;	// Diagnostic: error recovered

			// Clear in-retransmit flag since we're giving up
			sg_bInRetransmit = false;
		}
		else
		{
			// No completion or error yet, decrement timeout counter
			sg_u8Busy--;

			// If timeout expired, force clear
			if (sg_u8Busy == 0)
			{
				// Clear any pending status and disable the MOB
				CANSTMOB = 0x00;
				CANCDMOB = 0x00;	// Disable the MOB

				// Clear in-retransmit flag since we're giving up
				sg_bInRetransmit = false;

				// Disable the MOB interrupt to prevent spurious interrupts
				CANIE2 &= ~(1 << CANMOB_TX_IDX);

				sg_u16TxTimeouts++;	// Diagnostic: timeout occurred
			}
		}

		// Restore MOB
		CANPAGE = savedMOB;
	}
}

uint16_t CANGetTxTimeouts(void)
{
	return sg_u16TxTimeouts;
}

uint16_t CANGetTxErrors(void)
{
	return sg_u16TxErrors;
}

uint16_t CANGetTxOkPolled(void)
{
	return sg_u16TxOkPolled;
}

uint16_t CANGetBusOffEvents(void)
{
	return sg_u16BusOffEvents;
}

uint8_t CANGetTEC(void)
{
	return CANTEC;
}

uint8_t CANGetREC(void)
{
	return CANREC;
}

uint8_t CANGetTxOnlyErrorCount(void)
{
	return sg_u8TxOnlyErrorCount;
}

uint8_t CANGetTxBackoffDelay(void)
{
	return sg_u8TxBackoffDelay;
}

void CANCheckHealth(void)
{
	// Decrement bus-off recovery delay if active
	if (sg_u8BusOffRecoveryDelay > 0)
	{
		sg_u8BusOffRecoveryDelay--;
	}

	// Decrement TX backoff delay if active
	if (sg_u8TxBackoffDelay > 0)
	{
		sg_u8TxBackoffDelay--;
	}

	// Store current error counter values for diagnostics
	static uint8_t lastTEC = 0;
	static uint8_t lastREC = 0;
	uint8_t currentTEC = CANTEC;
	uint8_t currentREC = CANREC;

	// Detect TX-only errors (TEC increasing but REC stays at 0)
	// This indicates the module can't transmit but isn't seeing bus activity
	// Likely a hardware issue with TX circuitry or transceiver
	if ((currentTEC > lastTEC) && (currentREC == 0) && (lastREC == 0))
	{
		sg_u8TxOnlyErrorCount++;

		// If we have persistent TX-only errors, apply adaptive backoff
		if (sg_u8TxOnlyErrorCount > 3)
		{
			// Exponential backoff: 2, 4, 8, 16 ticks (200ms to 1.6s)
			if (sg_u8TxBackoffDelay == 0)
			{
				sg_u8TxBackoffDelay = 2 << ((sg_u8TxOnlyErrorCount - 3) > 3 ? 3 : (sg_u8TxOnlyErrorCount - 3));
				if (sg_u8TxBackoffDelay > 16)
				{
					sg_u8TxBackoffDelay = 16;	// Cap at 1.6 seconds
				}
			}
		}
	}
	else if (currentREC > 0)
	{
		// We're seeing bus activity - reset TX-only error counter
		sg_u8TxOnlyErrorCount = 0;
	}

	// Check if error counters are increasing rapidly (sign of bus problems)
	if ((currentTEC > lastTEC + 10) || (currentREC > lastREC + 10))
	{
		// Rapid error increase - likely physical bus problem
		// Apply temporary backoff
		if (sg_u8TxBackoffDelay < 5)
		{
			sg_u8TxBackoffDelay = 5;	// 500ms backoff for rapid errors
		}
	}

	lastTEC = currentTEC;
	lastREC = currentREC;

	// Check if CAN controller is in error passive state
	// TEC (Transmit Error Counter) or REC (Receive Error Counter) > 127
	if ((currentTEC > 127) || (currentREC > 127))
	{
		sg_u16ErrorPassive++;
	}

	// Check if near bus-off (TEC > 240)
	if (currentTEC > 240)
	{
		// Very close to bus-off (255) - try to prevent it
		// Could temporarily stop transmitting to let errors clear
	}

	// Check if CAN is disabled (should always be enabled)
	if (!(CANGSTA & (1 << ENFG)))
	{
		// CAN controller is disabled - re-enable it!
		CANGCON = (1 << ENASTB);

		// Re-initialize RX MOB since controller was disabled
		CANMOBSet(CANMOB_RX_IDX, &sg_sMOBGenericReceive, NULL, 0);

		// After bus-off recovery, error counters should be at 0
		// If they're not, there's still a bus problem
		if ((CANTEC > 0) || (CANREC > 0))
		{
			// Still have errors after re-enable - bus problem persists
		}
	}

	// Check if RX MOB is still enabled
	uint8_t savedMOB = CANPAGE;
	CANPAGE = CANMOB_RX_IDX << MOBNB0;

	// If RX MOB is disabled (CONMOB bits are 0), re-enable it
	if ((CANCDMOB & 0xC0) == 0)
	{
		// RX MOB is disabled - this shouldn't happen!
		// Re-enable it
		CANPAGE = savedMOB;  // Restore first
		CANMOBSet(CANMOB_RX_IDX, &sg_sMOBGenericReceive, NULL, 0);
	}
	else
	{
		CANPAGE = savedMOB;  // Restore MOB
	}
}

// Process RX message queue - call from main loop
// This processes all queued CAN messages by calling the registered callback
// Moves heavy application processing out of ISR to dramatically reduce interrupt latency
void CANProcessQueue(void)
{
	while (sg_rxQueueTail != sg_rxQueueHead)
	{
		// Get message from queue
		CANRxMessage* msg = &sg_rxQueue[sg_rxQueueTail];

		// Call the registered callback with the queued message
		if (sg_pfRXCallback)
		{
			sg_pfRXCallback(msg->eType, msg->u8Data, msg->u8DataLen);
		}

		// Advance tail pointer (consume message)
		sg_rxQueueTail = (sg_rxQueueTail + 1) % CAN_RX_QUEUE_SIZE;
	}
}

// Check and reconfigure RX MOBs if needed - call from main loop
// This defers the heavy MOB reconfiguration work out of ISR
void CANCheckMOBs(void)
{
	if (sg_bMOB0NeedsReconfigure)
	{
		CANMOBSet(CANMOB_RX_IDX, &sg_sMOBGenericReceive, NULL, 0);
		sg_bMOB0NeedsReconfigure = false;
	}

	if (sg_bMOB2NeedsReconfigure)
	{
		CANMOBSet(2, &sg_sMOBGenericReceive, NULL, 0);
		sg_bMOB2NeedsReconfigure = false;
	}
}

// Check and process TX retries if needed - call from main loop
// This defers TX retry logic out of ISR for reduced interrupt latency
void CANCheckRetry(void)
{
	if (sg_bRetryPending)
	{
		sg_bInRetransmit = true;
		CANSendMessageInternal(sg_eLastTXType, sg_u8LastTXData, sg_u8LastTXDataLen, true);
		sg_bRetryPending = false;
	}
}

// Get RX queue overflow count - diagnostic function
uint16_t CANGetRxQueueOverflows(void)
{
	return sg_u16RxQueueOverflows;
}
