dp-web4/ModuleCPU/STORE.h

#ifndef _STORE_H_
#define _STORE_H_

#include <stdint.h>
#include <stdbool.h>
#include <stddef.h>  // For offsetof macro
#include <adc.h>
#include <vUART.h>

// Define constants
#define SECTOR_SIZE 512
#define MAX_CELLS 108  // this may change later - dp




// Global state structure (Sector 0) - MUST BE 4-BYTE ALIGNED FOR 32-BIT XFERS
typedef struct __attribute__((aligned(4))) {
	uint64_t lastUpdateTimestamp;
	uint32_t checksum;
	uint32_t firstSessionSector;
	uint32_t lastSessionSector;
	uint32_t sessionCount;
	uint32_t newSessionSector;
	uint32_t activeSessionMapSector;
	uint32_t activeSessionMapOffset;
	uint8_t cellDataDescriptor[16];  // Placeholder size, adjust as needed
	uint8_t frameDataDescriptor[32]; // Placeholder size, adjust as needed
	uint8_t cellCount;
	uint8_t cellStructuresPerFrame;
	uint8_t lifetimeStats[384];      // Placeholder size, adjust as needed
} GlobalState;

// Cell data structure - MUST BE 4-BYTE ALIGNED FOR 32-BIT XFERS
// Contains RAW data from CellCPU in native format (not converted)
typedef struct __attribute__((aligned(4))) {
	uint16_t voltage;       // RAW 10-bit ADC value from CellCPU (0-1023)
	                        // Requires conversion: see CellDataConvertVoltage() in main.c
	                        // Formula: (adc_value / 1024) * VREF / VOLTAGE_SCALE * CAL_FACTOR
	int16_t temperature;    // RAW MCP9843 format from CellCPU (signed 8.4 fixed point)
	                        // Bits 0-3: 16ths of degree C (fractional)
	                        // Bits 4-11: Whole degrees C
	                        // Bit 12: Sign bit (0=positive, 1=negative)
	                        // Bit 15: I2C status (0x8000 = MSG_CELL_TEMP_I2C_OK)
	                        // Requires conversion: see CellDataConvertTemperature() in main.c
} CellData;

// Invalid cell markers - indicates cell didn't report in this reading
#define INVALID_CELL_VOLTAGE  0xFFFF
#define INVALID_CELL_TEMP     0x7FFF  // Max int16_t value


typedef struct
{
	bool bValid;
	uint16_t u16Reading;
} SADCReading;

#define FRAME_VALID_SIG 0xBA77
#define FRAME_VERSION 1  // Frame format version number

// Frame metadata structure - contains all the control and status fields
typedef struct __attribute__((aligned(4))) {
	uint16_t validSig;  // if != FRAME_VALID_SIG then frame is not valid (0xBA77)
	uint8_t version;    // Frame format version (for future compatibility)
	uint8_t cellBufferStart;  // Offset from start of frame to cell data buffer (4-byte aligned, max 255)
	uint16_t frameBytes;  // actual number of bytes per frame, for diagnostics
	uint64_t timestamp;
	uint32_t moduleUniqueId;  // unique ID for this module (from EEPROM)

// session variables, survive frame write
	uint8_t sg_u8WDTCount;  // number of WDT resets in current session
	uint8_t sg_u8CellCPUCountFewest;   // for the frame (min across all string readings in frame)
	uint8_t sg_u8CellCPUCountMost;     // for the frame (max across all string readings in frame)
	uint8_t sg_u8CellCountExpected;

	uint16_t u16maxCurrent;  // session current is in units of 0.02A relative to CURRENT_FLOOR	-655.36
	uint16_t u16minCurrent;
	uint16_t u16avgCurrent;
	uint8_t sg_u8CurrentBufferIndex;
	// ADC calibration parameters (calculated constants, not measured values)
	int32_t sg_i32VoltageStringMin;  // ADC range floor (2.25V/cell × cell count) in millivolts
	int32_t sg_i32VoltageStringMax;  // ADC range ceiling (4.5V/cell × cell count) in millivolts
	int16_t sg_i16VoltageStringPerADC;  // ADC scaling factor in ADC_VOLT_FRACTION (1/128) fractions of millivolts

//	frame variables, reset after frame write
	bool bDischargeOn;
	uint16_t sg_u16CellCPUI2CErrors;
	uint8_t sg_u8CellFirstI2CError;
	uint16_t sg_u16BytesReceived;
	uint8_t sg_u8CellCPUCount;     // for the frame
	uint8_t sg_u8MCRXFramingErrors;
	uint8_t sg_u8LastCompleteCellCount;  // Cell count from last complete frame (for MODULE_DETAIL responses)

// processed data, calculated at start of each WRITE frame
// NOTE: These statistics contain CONVERTED values (not raw CellData format)
	uint16_t u16frameCurrent;
	int16_t sg_s16HighestCellTemp;	//  CONVERTED: 100ths of °C with TEMPERATURE_BASE offset (5535 = 0°C)
	int16_t sg_s16LowestCellTemp;   //  CONVERTED: 100ths of °C with TEMPERATURE_BASE offset (5535 = 0°C)
	int16_t sg_s16AverageCellTemp;	//  CONVERTED: 100ths of °C with TEMPERATURE_BASE offset (5535 = 0°C)
	uint16_t sg_u16HighestCellVoltage;  // CONVERTED: in millivolts (e.g., 3450 = 3.45V)
	uint16_t sg_u16LowestCellVoltage;   // CONVERTED: in millivolts (e.g., 3450 = 3.45V)
	uint16_t sg_u16AverageCellVoltage;  // CONVERTED: in millivolts (e.g., 3450 = 3.45V)
	uint32_t sg_u32CellVoltageTotal;	// CONVERTED: All cell voltages added up, in millivolts

	int32_t sg_i32VoltageStringTotal;  // in 15mv increments, from ADC

// ADC stuff
	SADCReading ADCReadings[ EADCTYPE_COUNT ];

// New circular buffer management fields
	uint32_t frameCounter;          // Persistent frame counter (persisted in EEPROM with wear leveling)
	uint16_t nstrings;              // Number of string readings that can fit in buffer
	uint16_t currentIndex;          // Current position in circular buffer (0 to nstrings-1)
	uint16_t readingCount;          // Number of valid readings in buffer
} FrameMetadata;

// Frame data structure - MUST BE 4-BYTE ALIGNED FOR 32-BIT XFERS
typedef struct __attribute__((aligned(4))) {
	FrameMetadata m;  // All metadata fields (statistics are CONVERTED values)
	uint8_t c[1024 - sizeof(FrameMetadata)];  // Circular buffer containing RAW CellData structures
	                                          // Cell data stored at offset m.cellBufferStart from frame start
	                                          // Contains m.readingCount string readings, each with
	                                          // m.sg_u8CellCountExpected cells in RAW format (unconverted)
} FrameData;

// Helper functions for accessing cell data in the buffer

// Get pointer to a specific string reading slot (0 to nstrings-1)
static inline CellData* GetStringDataAtIndex(FrameData* frame, uint16_t index) {
	uint16_t bytes_per_string = frame->m.sg_u8CellCountExpected * sizeof(CellData);
	uint16_t offset = index * bytes_per_string;
	return (CellData*)(&frame->c[offset]);
}

static inline volatile CellData* GetStringDataAtIndexVolatile(volatile FrameData* frame, uint16_t index) {
	uint16_t bytes_per_string = frame->m.sg_u8CellCountExpected * sizeof(CellData);
	uint16_t offset = index * bytes_per_string;
	return (volatile CellData*)(&frame->c[offset]);
}

// Get pointer to current writing slot
static inline CellData* GetStringData(FrameData* frame) {
	return GetStringDataAtIndex(frame, frame->m.currentIndex);
}

static inline volatile CellData* GetStringDataVolatile(volatile FrameData* frame) {
	return GetStringDataAtIndexVolatile(frame, frame->m.currentIndex);
}

// Get pointer to most recent complete reading (for CAN responses)
static inline volatile CellData* GetLatestCompleteString(volatile FrameData* frame) {
	// If we have at least one complete reading, return the previous slot
	if (frame->m.readingCount > 0) {
		uint16_t lastIndex = (frame->m.currentIndex == 0) ?
		                     (frame->m.nstrings - 1) :
		                     (frame->m.currentIndex - 1);
		return GetStringDataAtIndexVolatile(frame, lastIndex);
	}
	// Otherwise return current slot (may be incomplete)
	return GetStringDataVolatile(frame);
}

// Define the desired frame size to be exactly 2 sectors (1024 bytes)
#define FRAME_SIZE_TARGET 1024

// Calculate the actual cell buffer size
#define FRAME_CELLBUFFER_SIZE 896

#define SECTORS_PER_FRAME 2  // Always 2 sectors (1024 bytes)
#define FRAME_BUFFER_SIZE 1024  // Exactly 1024 bytes

// Verify frame size at compile time
#define STATIC_ASSERT(COND,MSG) typedef char static_assertion_##MSG[(COND)?1:-1]
STATIC_ASSERT(sizeof(FrameData) == FRAME_BUFFER_SIZE, frame_size_mismatch);


// Function prototypes
bool STORE_Init(void);
bool STORE_WriteFrame(volatile FrameData* frame, bool bSDCardReady, bool bSDWriteEnabled);
bool STORE_ReadFrameByCounter(uint32_t frameCounter);  // Read frame from SD by counter into frameBuffer
bool STORE_StartNewSession(void);
bool STORE_EndSession(void);
bool STORE_GetSessionCount(uint32_t* count);
bool STORE_GetSessionInfo(uint32_t sessionIndex, uint32_t* startSector, uint32_t* sectorCount);
uint8_t* STORE_GetFrameBuffer(void);  // Get pointer to internal frame buffer for CAN frame transfer


#endif
